dawidmpunkt/rumble-for-steamdeck/pictures/left-daughterboard-map2.jpg

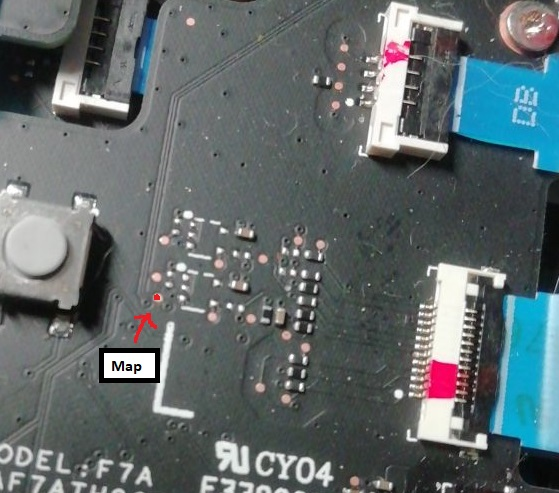
pictures/left-daughterboard-map2.jpg
