dawidmpunkt/rumble-for-steamdeck/pictures/left-daughterboard-map.jpg

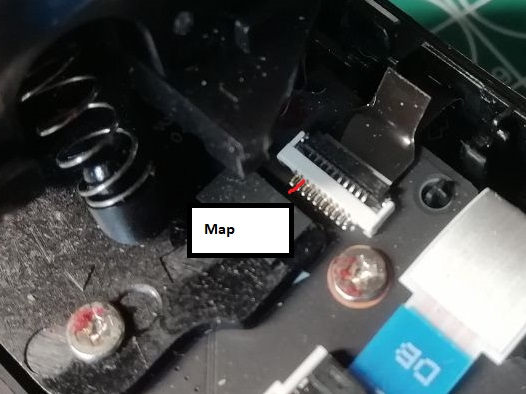
pictures/left-daughterboard-map.jpg
