dawidmpunkt/rumble-for-steamdeck/pictures/right-daughterboard-menu.jpg

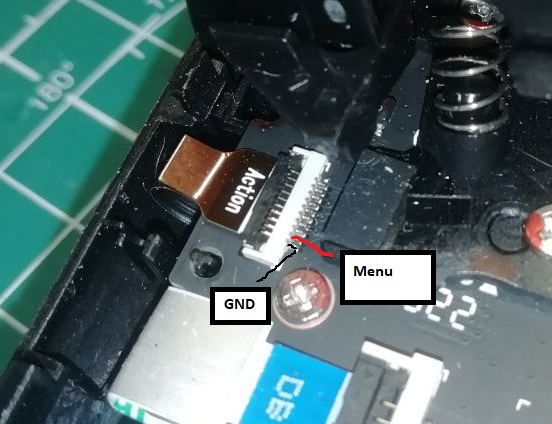
pictures/right-daughterboard-menu.jpg
