dawidmpunkt/rumble-for-steamdeck/pictures/RumbleBoard/RumbleBoard_v01.jpg

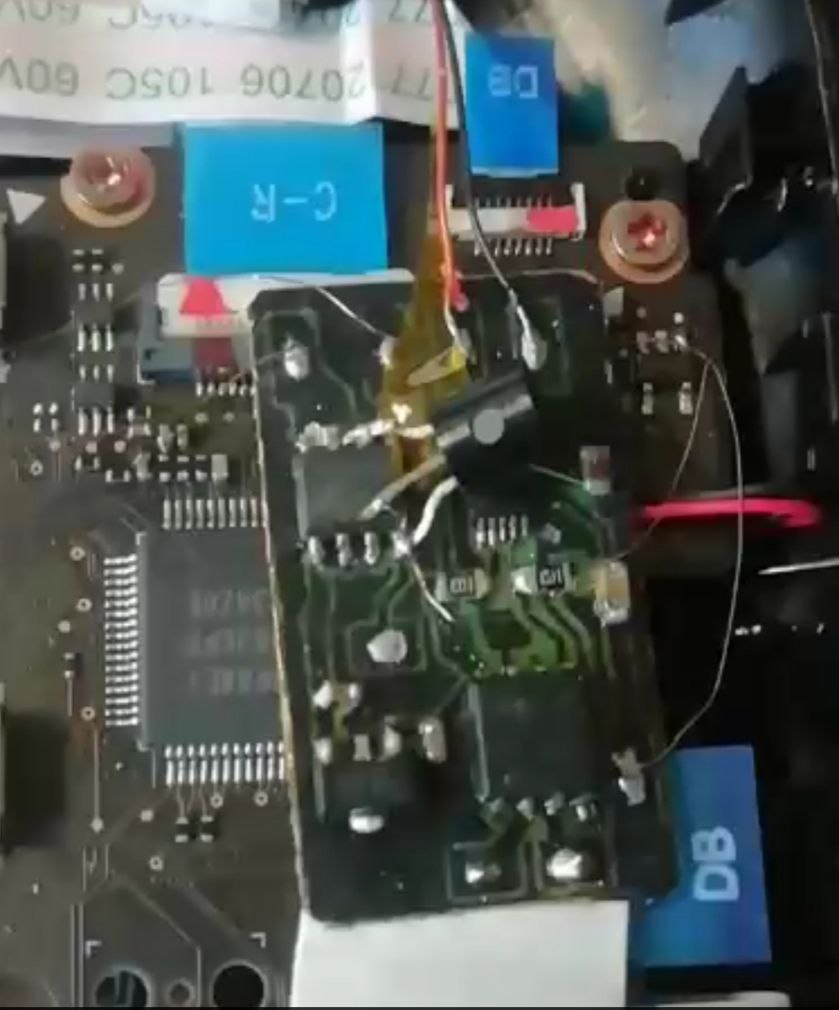
pictures/RumbleBoard/RumbleBoard_v01.jpg
