dawidmpunkt/rumble-for-steamdeck/pictures/RumbleBoard/RumbleBoard_v02.jpg

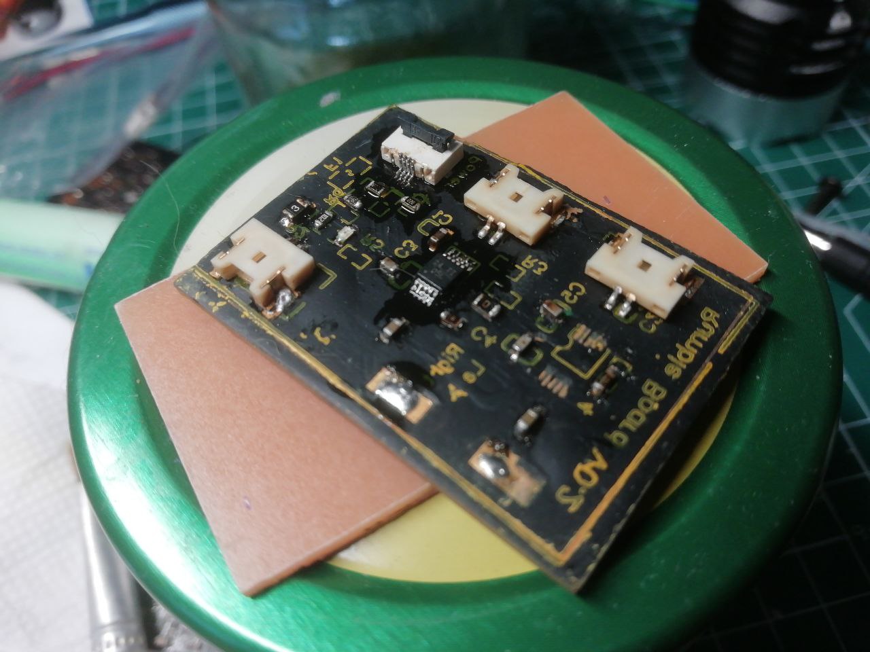
pictures/RumbleBoard/RumbleBoard_v02.jpg
