dawidmpunkt/rumble-for-steamdeck/pictures/RumbleBoard/RumbleBoard_V02_.jpg

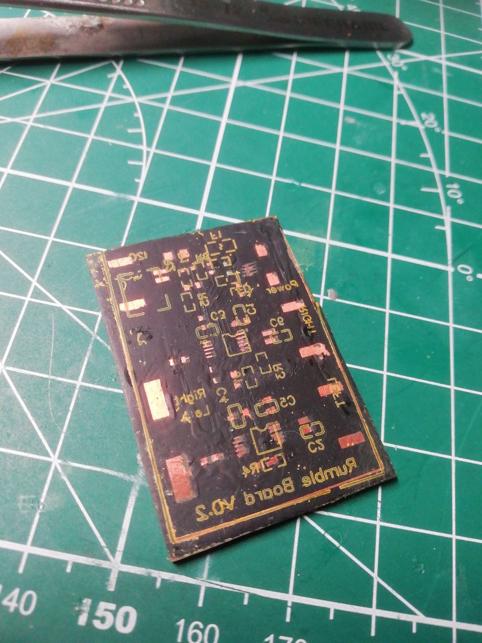
pictures/RumbleBoard/RumbleBoard_V02_.jpg
