dawidmpunkt/rumble-for-steamdeck/pictures/RumbleBoard/RumbleBoard_v03.jpg

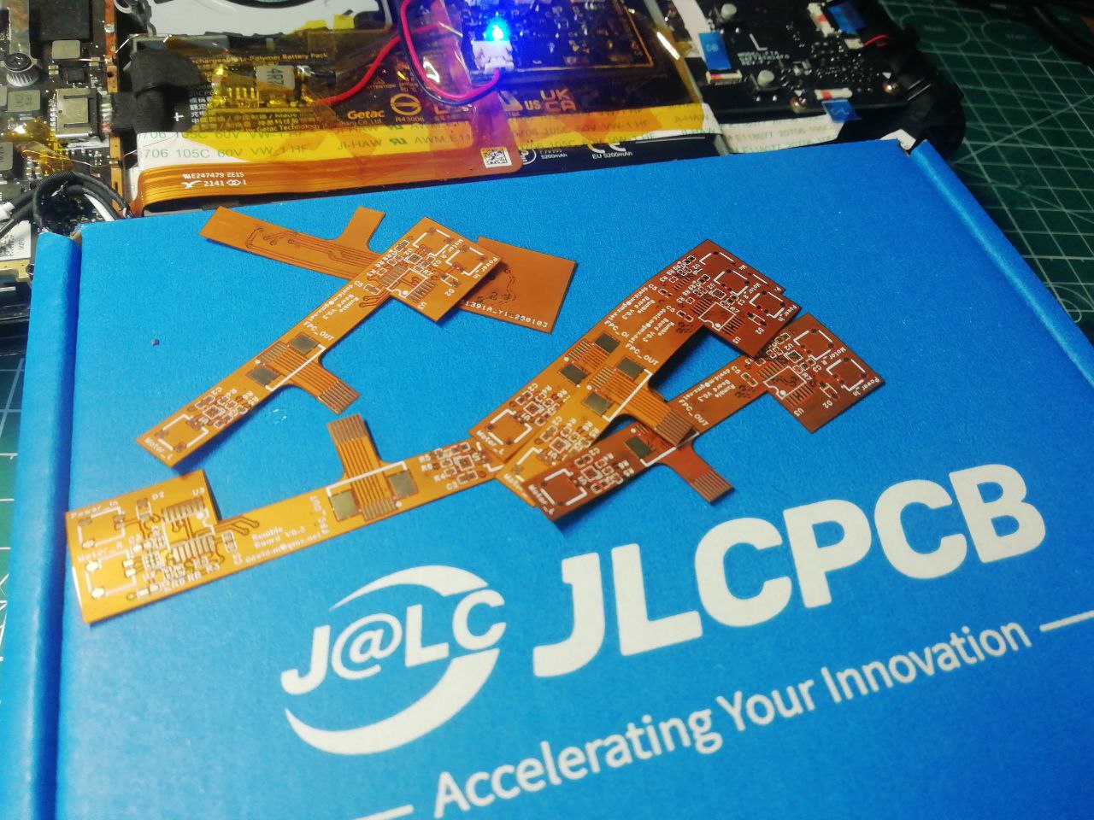
pictures/RumbleBoard/RumbleBoard_v03.jpg
