dawidmpunkt/rumble-for-steamdeck/pictures/RumbleBoard/RumbleBoard_v03_and_RumbleStick.jpg

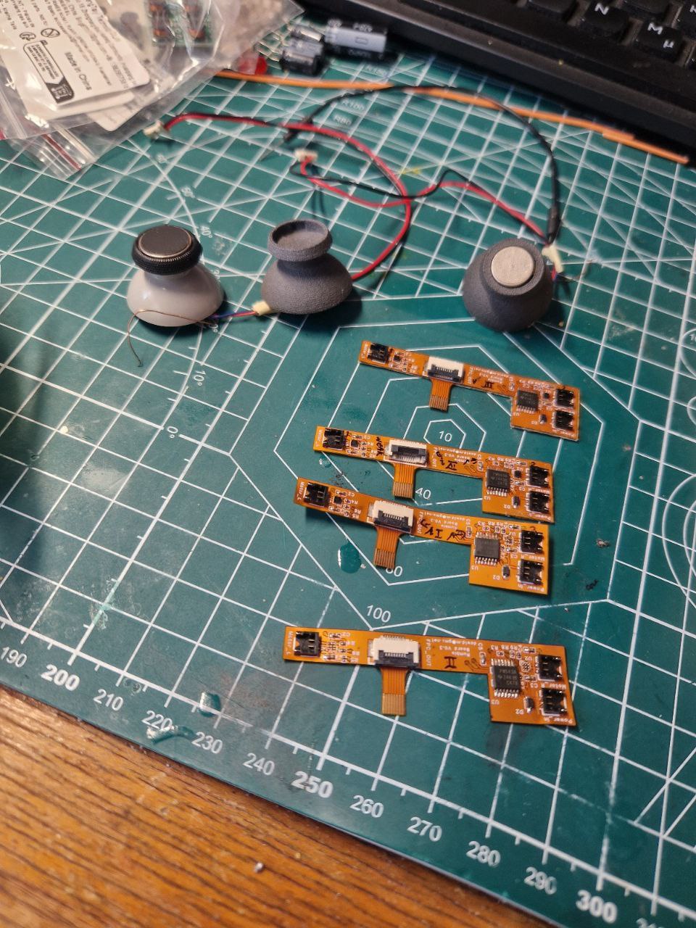
pictures/RumbleBoard/RumbleBoard_v03_and_RumbleStick.jpg
