dawidmpunkt/rumble-for-steamdeck/pictures/RumbleBoard/RumbleBoard_v03_dummy.jpg

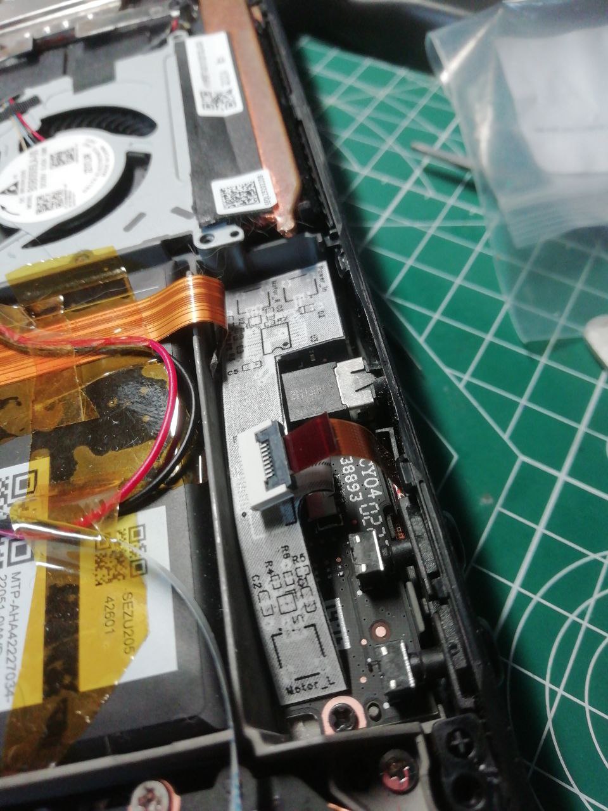
pictures/RumbleBoard/RumbleBoard_v03_dummy.jpg
