dawidmpunkt/rumble-for-steamdeck/pictures/RumbleStick/RumbleStick-10mm.jpg

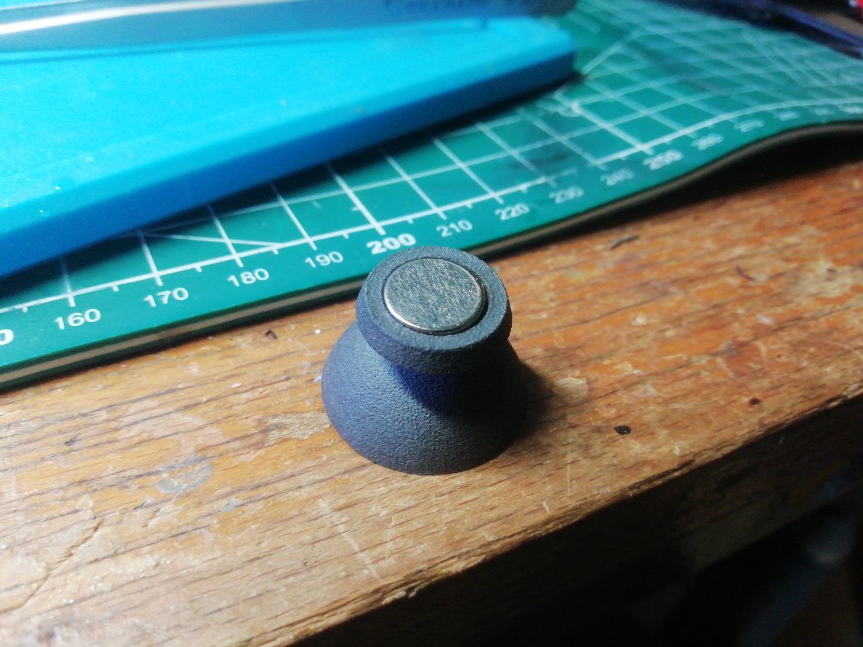
pictures/RumbleStick/RumbleStick-10mm.jpg
