dawidmpunkt/rumble-for-steamdeck/pictures/RumbleStick/RumbleStick-prototype.jpg

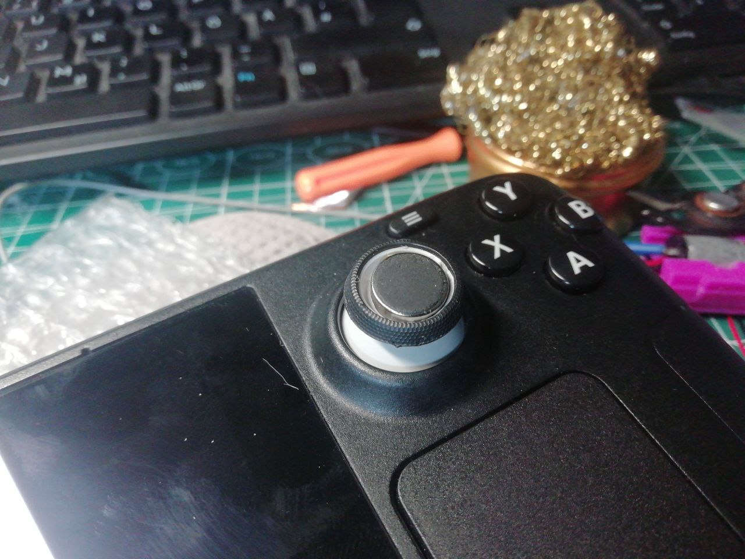
pictures/RumbleStick/RumbleStick-prototype.jpg
