dawidmpunkt/rumble-for-steamdeck/pictures/RumbleStick/RumbleStick-variants.jpg

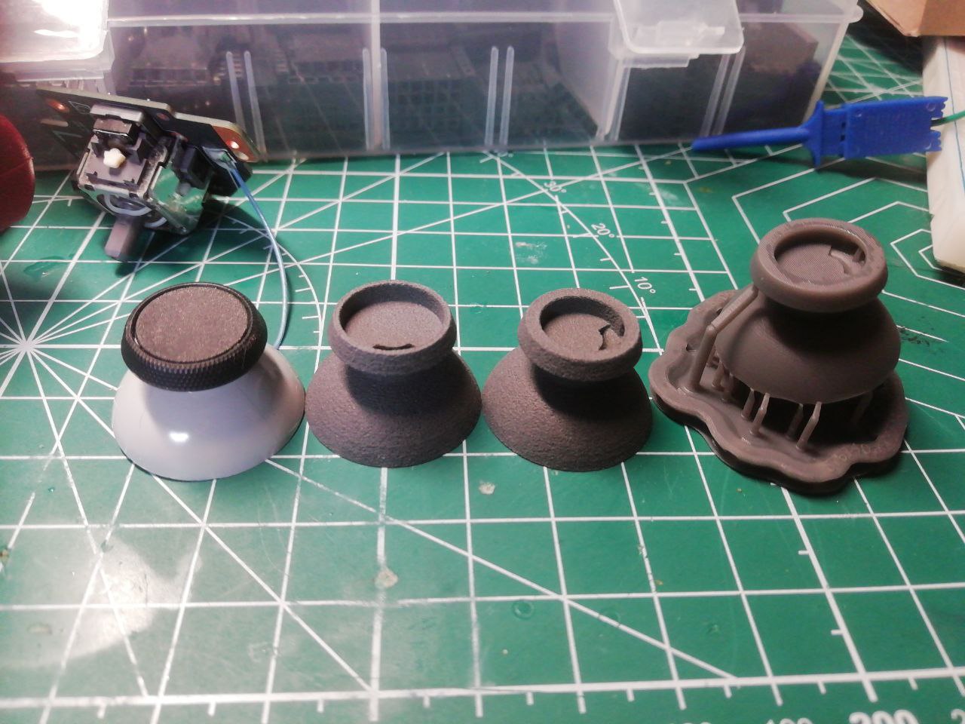
pictures/RumbleStick/RumbleStick-variants.jpg
