dawidmpunkt/rumble-for-steamdeck/pictures/RumbleStick/RumbleStick_.jpg

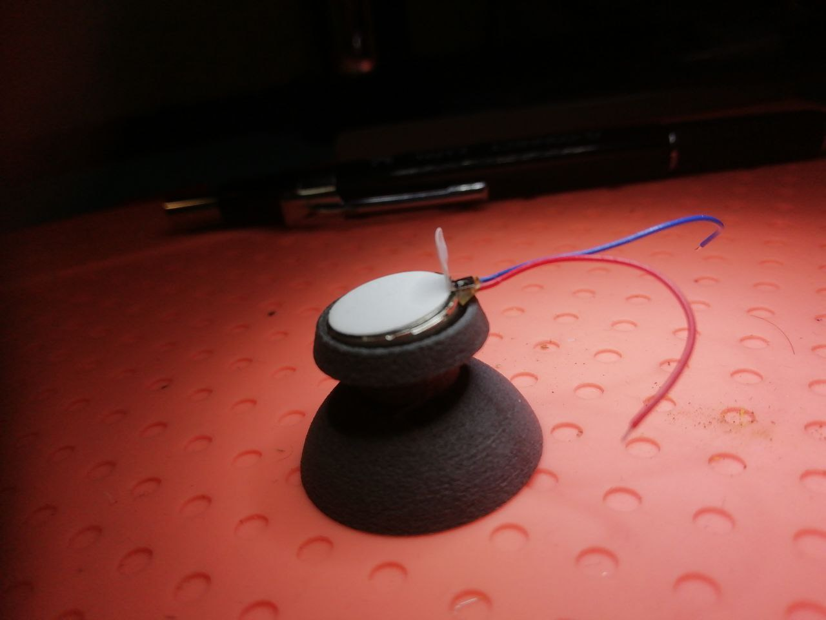
pictures/RumbleStick/RumbleStick_.jpg
