dawidmpunkt/rumble-for-steamdeck/pictures/RumbleStick/SLS_vs_SLA.jpg

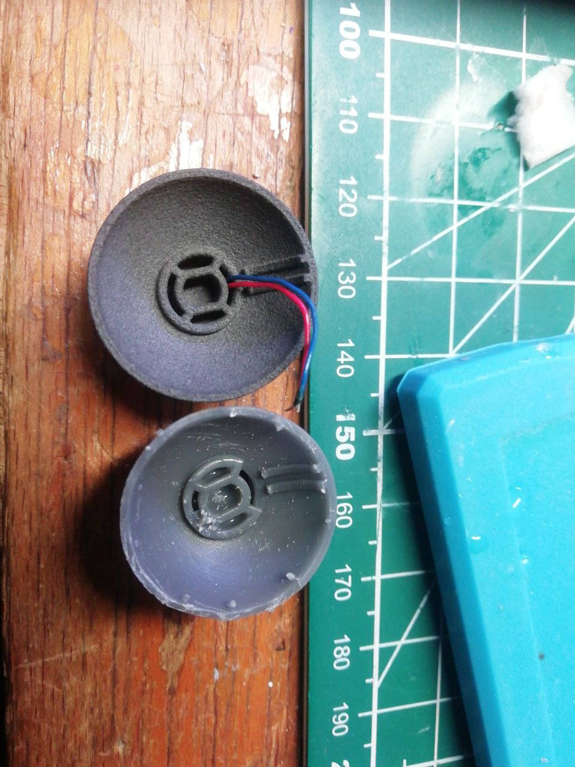
pictures/RumbleStick/SLS_vs_SLA.jpg
