dawidmpunkt/rumble-for-steamdeck/pictures/DRV2605L_wiring.jpg

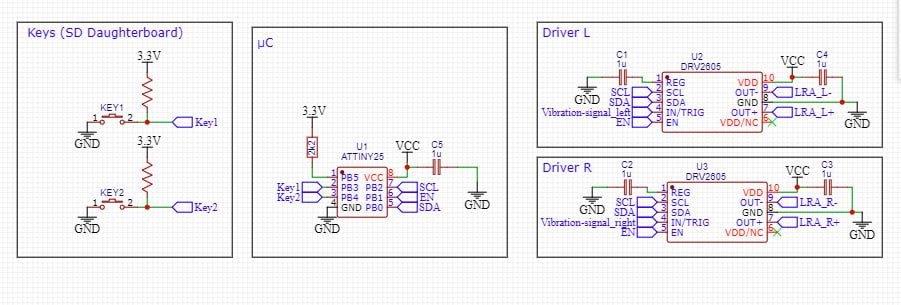
pictures/DRV2605L_wiring.jpg
