dawidmpunkt/rumble-for-steamdeck/pictures/RumbleBoard/RumbleBoard_v02_wiring.jpg

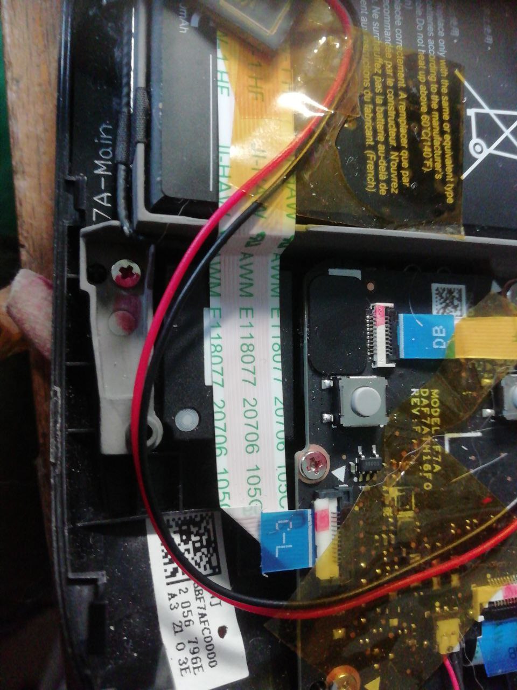
pictures/RumbleBoard/RumbleBoard_v02_wiring.jpg
