dawidmpunkt/rumble-for-steamdeck/pictures/RumbleBoard/RumbleBoard_v02_wiring_.jpg

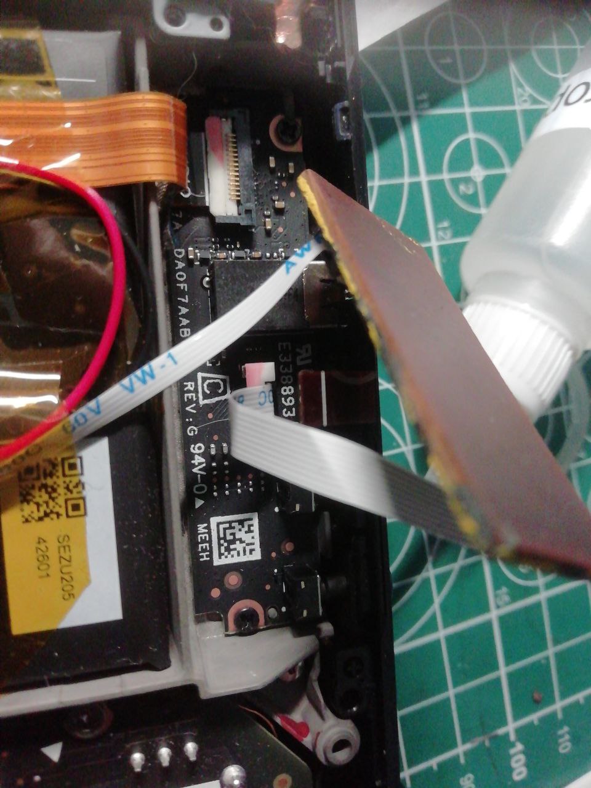
pictures/RumbleBoard/RumbleBoard_v02_wiring_.jpg
