dawidmpunkt/rumble-for-steamdeck/pictures/RumbleBoard/RumbleBoard_v02_wiring__.jpg

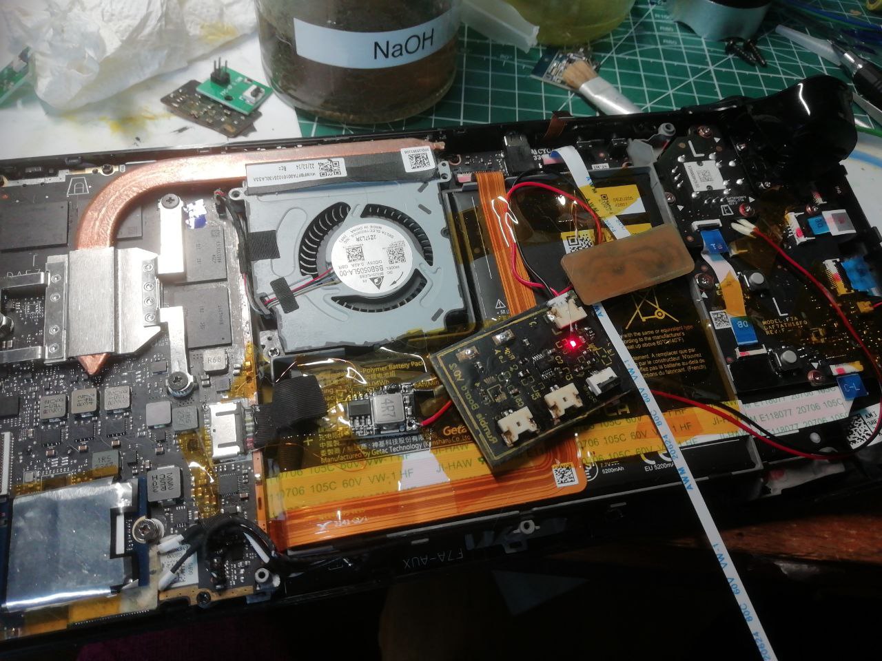
pictures/RumbleBoard/RumbleBoard_v02_wiring__.jpg
